Espeer5/digir/src/BPM/mcu/digir_bpm_fw/CM4/Core/Inc/main.h

#define FDCAN2_RX_Pin GPIO_PIN_5
#define FDCAN2_RX_GPIO_Port GPIOB
#define SDIO1_D2_Pin GPIO_PIN_10
#define SDIO1_D2_GPIO_Port GPIOC
#define MII_TX_EN_Pin GPIO_PIN_11
#define MII_TX_EN_GPIO_Port GPIOG
#define LCD_DISP_Pin GPIO_PIN_15
#define LCD_DISP_GPIO_Port GPIOJ
#define SDIO1_D3_Pin GPIO_PIN_11
#define SDIO1_D3_GPIO_Port GPIOC
#define FDCAN2_RXH14_Pin GPIO_PIN_14
#define FDCAN2_RXH14_GPIO_Port GPIOH
#define OSC32_OUT_Pin GPIO_PIN_15
#define OSC32_OUT_GPIO_Port GPIOC
#define OSC32_IN_Pin GPIO_PIN_14
#define OSC32_IN_GPIO_Port GPIOC
#define MII_TXD3_Pin GPIO_PIN_2
#define MII_TXD3_GPIO_Port GPIOE
#define MII_TXD1_Pin GPIO_PIN_12
#define MII_TXD1_GPIO_Port GPIOG
#define SDIO1_CK_Pin GPIO_PIN_12
#define SDIO1_CK_GPIO_Port GPIOC
#define SDIO1_D5_Pin GPIO_PIN_9
#define SDIO1_D5_GPIO_Port GPIOB
#define SDIO1_D4_Pin GPIO_PIN_8
#define SDIO1_D4_GPIO_Port GPIOB
#define MII_TXD0_Pin GPIO_PIN_13
#define MII_TXD0_GPIO_Port GPIOG
#define SDIO1_CMD_Pin GPIO_PIN_2
#define SDIO1_CMD_GPIO_Port GPIOD
#define VBUS_FS2_Pin GPIO_PIN_9
#define VBUS_FS2_GPIO_Port GPIOA
#define FDCAN1_TX_Pin GPIO_PIN_13
#define FDCAN1_TX_GPIO_Port GPIOH
#define SDIO1_D0_Pin GPIO_PIN_8
#define SDIO1_D0_GPIO_Port GPIOC
#define SDIO1_D1_Pin GPIO_PIN_9
#define SDIO1_D1_GPIO_Port GPIOC
#define USB_OTG_FS2_P_Pin GPIO_PIN_12
#define USB_OTG_FS2_P_GPIO_Port GPIOA
#define USB_OTG_FS2_N_Pin GPIO_PIN_11
#define USB_OTG_FS2_N_GPIO_Port GPIOA
#define MII_RX_ER_Pin GPIO_PIN_10
#define MII_RX_ER_GPIO_Port GPIOI
#define SDIO1_D7_Pin GPIO_PIN_7
#define SDIO1_D7_GPIO_Port GPIOC
#define SDIO1_D6_Pin GPIO_PIN_6
#define SDIO1_D6_GPIO_Port GPIOC
#define OSC_OUT_Pin GPIO_PIN_1
#define OSC_OUT_GPIO_Port GPIOH
#define OSC_IN_Pin GPIO_PIN_0
#define OSC_IN_GPIO_Port GPIOH
#define MII_MDC_Pin GPIO_PIN_1
#define MII_MDC_GPIO_Port GPIOC
#define MII_TXD2_Pin GPIO_PIN_2
#define MII_TXD2_GPIO_Port GPIOC
#define MII_TX_CLK_Pin GPIO_PIN_3
#define MII_TX_CLK_GPIO_Port GPIOC
#define MII_CRS_Pin GPIO_PIN_2
#define MII_CRS_GPIO_Port GPIOH
#define MII_MDIO_Pin GPIO_PIN_2
#define MII_MDIO_GPIO_Port GPIOA
#define MII_RX_CLK_Pin GPIO_PIN_1
#define MII_RX_CLK_GPIO_Port GPIOA
#define MII_COL_Pin GPIO_PIN_3
#define MII_COL_GPIO_Port GPIOH
#define MII_RX_DV_Pin GPIO_PIN_7
#define MII_RX_DV_GPIO_Port GPIOA
#define MII_RXD0_Pin GPIO_PIN_4
#define MII_RXD0_GPIO_Port GPIOC
#define MII_RXD3_Pin GPIO_PIN_1
#define MII_RXD3_GPIO_Port GPIOB
#define MII_RXD1_Pin GPIO_PIN_5
#define MII_RXD1_GPIO_Port GPIOC
#define MII_RXD2_Pin GPIO_PIN_0
#define MII_RXD2_GPIO_Port GPIOB
#define FDCAN2_TX_Pin GPIO_PIN_13
#define FDCAN2_TX_GPIO_Port GPIOB
