Espeer5/digir/src/BPM/mcu/digir_bpm_fw/CM7/App/Src/system_control.c

//#################################################################################################
//  DIGIR BPM CPU SYSTEM CONTROL
//
//  VERSION 0.1
//#################################################################################################

// This module contains definitions of common functions for control flow of the entire system

//#################################################################################################
//  CHANGE LOG
//#################################################################################################

// 7/31/26  Edward Speer  Initial revision

//#################################################################################################
//  INCLUDES
//#################################################################################################

#include "system_control.h"

//#################################################################################################
//  FUNCTIONS
//#################################################################################################

__attribute__((noreturn))                                                                           
void fatal_err()                                                                                    
{                                                                                                   
    __disable_irq();                                                                                
                                                                                                    
#ifdef DEBUG                                                                                        
                                                                                                    
    __BKPT(0);                                                                                      
                                                                                                    
    while (1)                                                                                       
    {                                                                                               
        __NOP();                                                                                    
    }                                                                                               
                                                                                                    
#else                                                                                               
                                                                                                    
    NVIC_SystemReset();                                                                             
                                                                                                    
    while (1) {}                                                                                    
                                                                                                    
#endif // #ifdef DEBUG                                                                              
}
