Espeer5/digir/src/BPM/mcu/digir_bpm_fw/CM7/App/Inc/system_control.h

//#################################################################################################
//  DIGIR BPM CMU SYSTEM CONTROL
//
//  VERSION 0.1
//#################################################################################################

// This module contains declarations of common functions for control flow of the entire system

//#################################################################################################
//  CHANGE LOG
//#################################################################################################

// 7/31/26  Edward Speer  Initial revision

//#################################################################################################
//  INCLUDES
//#################################################################################################

#include "stm32h7xx_hal.h"

//#################################################################################################
//  FUNCTIONS
//#################################################################################################

// Halt in debug mode, or reset the firmware in production
__attribute__((noreturn)) void fatal_err(void);
