Espeer5/digir/src/BPM/mcu/digir_bpm_fw/CM7/App/Inc/hal_callbacks.h

//#################################################################################################
//  DIGIR BPM MCU HAL CALLBCKS
//
//  VERSION 0.1
//#################################################################################################

// This module declares the callback handler functions for the STM32 HAL used by the DigiR BPM.

//#################################################################################################
//  CHANGE LOG
//#################################################################################################

// 7/29/26  Edward Speer  Initial revision

#ifndef HAL_CALLBACKS_H
#define HAL_CALLBACKS_H

//#################################################################################################
//  INCLUDES
//#################################################################################################

#include "stm32h7xx_hal.h"

//#################################################################################################
//  CALLBACKS
//#################################################################################################

void HAL_UART_RxCpltCallback(UART_HandleTypeDef *uart_handle);

#endif // #ifndef HAL_CALLBACKS_H
