Espeer5/digir/src/BPM/mcu/digir_bpm_fw/CM7/App/Src/hal_callbacks.c

//#################################################################################################
//  DIGIR BPM HAL CALLBACKS
//
//  VERSION 0.1
//#################################################################################################

// This module defines the callback handler functions for the STM32 HAL used by the DigiR BPM.

//#################################################################################################
//  CHANGE LOG
//#################################################################################################

// 7/29/26  Edward Speer  Initial revision

//#################################################################################################
//  INCLUDES
//#################################################################################################

#include "hal_callbacks.h"
#include "gnss_uart.h"

//#################################################################################################
//  CALLBACKS
//#################################################################################################

void HAL_UART_RxCpltCallback(UART_HandleTypeDef *uart_handle)
{
    if (uart_handle->Instance == USART1)
    {
        gnss_uart_reader_handle_byte(get_gnss_uart_reader());
    }
}
